goodtofufriday/megaman-battle--network-exe-chip-project/EXE 4 Advance Chips/Advance Chip Missing Labels/Black_Barrier_JPN.png

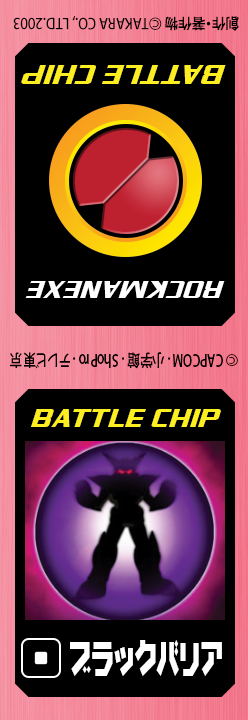
EXE 4 Advance Chips/Advance Chip Missing Labels/Black_Barrier_JPN.png
