goodtofufriday/megaman-battle--network-exe-chip-project/EXE 4 Advance Chips/Advance Chip Missing Labels/BurnerMan_ENG.png

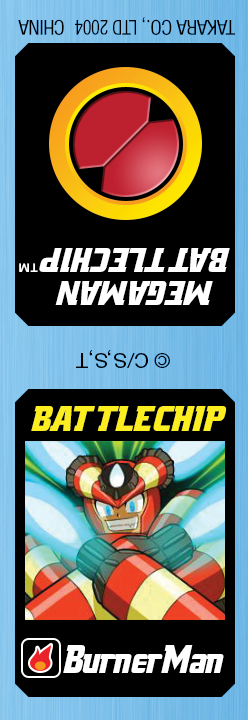
EXE 4 Advance Chips/Advance Chip Missing Labels/BurnerMan_ENG.png
