goodtofufriday/megaman-battle--network-exe-chip-project/EXE 4 Advance Chips/Advance Duo+GrandPrix Power Patch/image.png

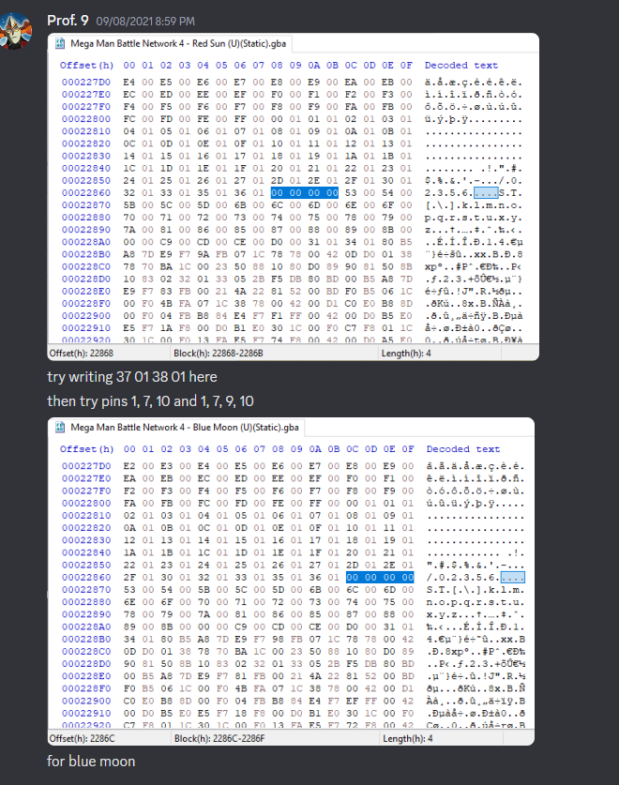
EXE 4 Advance Chips/Advance Duo+GrandPrix Power Patch/image.png
