goodtofufriday/megaman-battle--network-exe-chip-project/Plug-In Pet/Plug-In Pet Labels/0.jpg

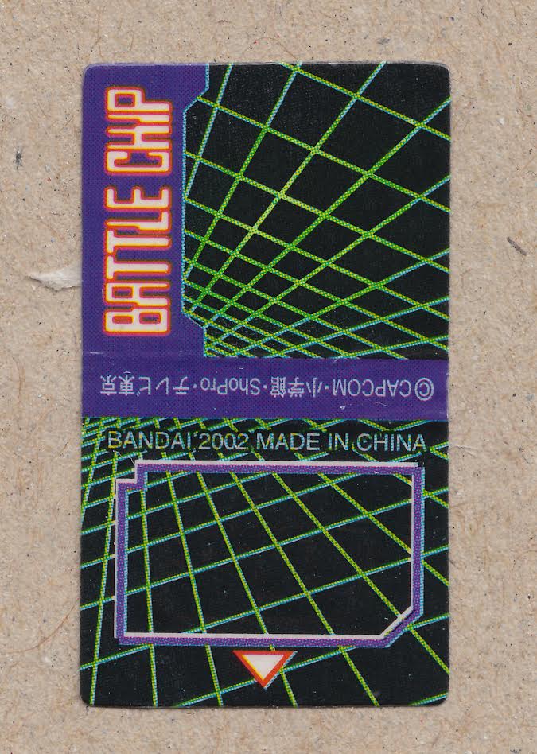
Plug-In Pet/Plug-In Pet Labels/0.jpg
