goodtofufriday/megaman-battle--network-exe-chip-project/Numbers/848.dxf

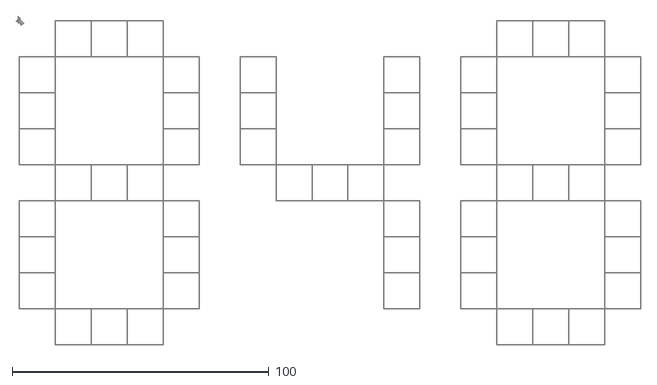
[picture p29: CAD file, 2023-03-07]
Numbers/848.dxf
243.4 x 127.9
