goodtofufriday/megaman-battle--network-exe-chip-project/Numbers/847.dxf

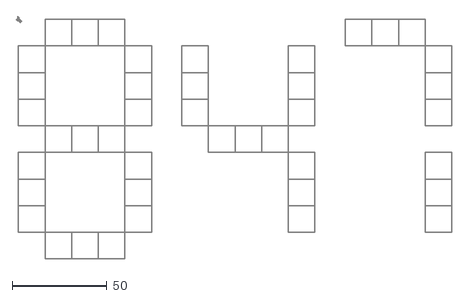
[picture p30: CAD file, 2023-03-07]
Numbers/847.dxf
229.6 x 128.0
