goodtofufriday/megaman-battle--network-exe-chip-project/Numbers/845.dxf

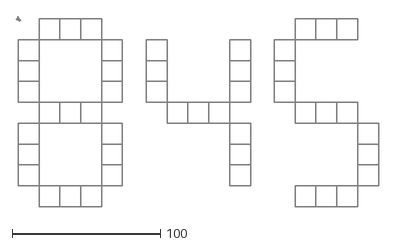
[picture p31: CAD file, 2023-03-07]
Numbers/845.dxf
244.0 x 128.2
