goodtofufriday/megaman-battle--network-exe-chip-project/Numbers/844.dxf

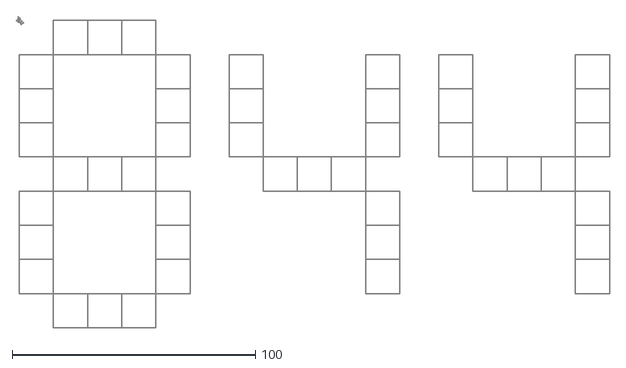
[picture p32: CAD file, 2023-03-07]
Numbers/844.dxf
244.0 x 128.2
