goodtofufriday/megaman-battle--network-exe-chip-project/Numbers/843.dxf

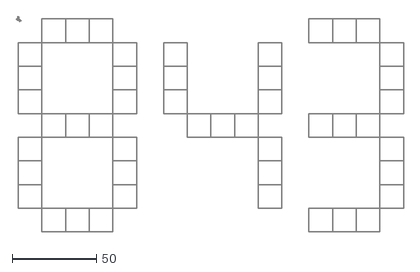
[picture p33: CAD file, 2023-03-07]
Numbers/843.dxf
230.1 x 128.3
