goodtofufriday/megaman-battle--network-exe-chip-project/Numbers/792.dxf

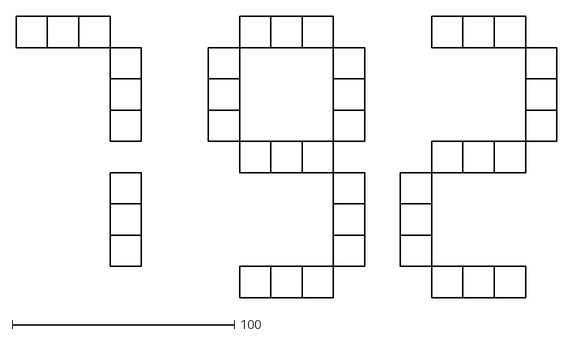
[picture p34: CAD file, 2023-03-07]
Numbers/792.dxf
243.0 x 126.6
