goodtofufriday/megaman-battle--network-exe-chip-project/Numbers/791.dxf

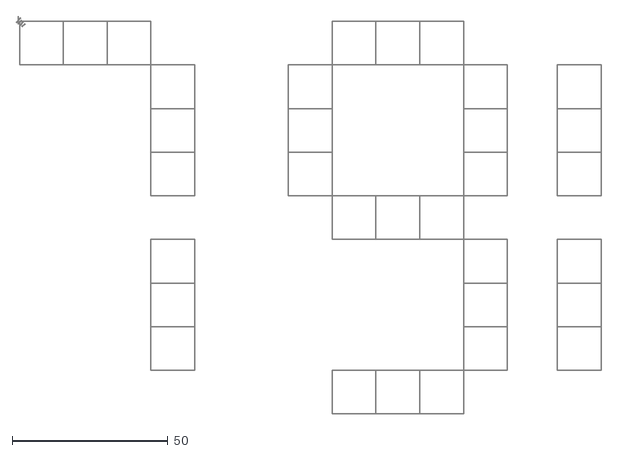
[picture p35: CAD file, 2023-03-07]
Numbers/791.dxf
188.0 x 127.9
