goodtofufriday/megaman-battle--network-exe-chip-project/Numbers/790.dxf

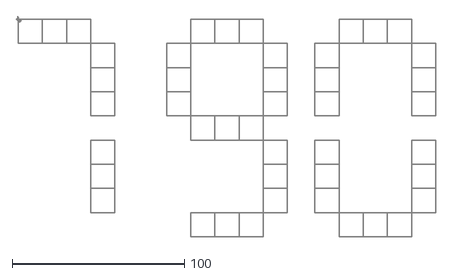
[picture p36: CAD file, 2023-03-07]
Numbers/790.dxf
243.8 x 128.1
