goodtofufriday/megaman-battle--network-exe-chip-project/Numbers/731.dxf

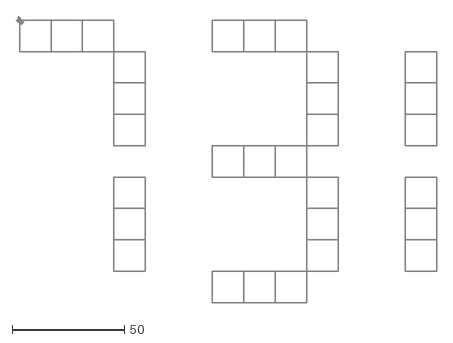
[picture p37: CAD file, 2023-03-07]
Numbers/731.dxf
187.4 x 127.7
