goodtofufriday/megaman-battle--network-exe-chip-project/Numbers/727.dxf

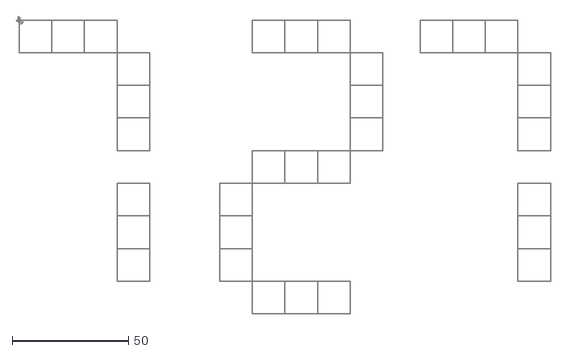
[picture p38: CAD file, 2023-03-07]
Numbers/727.dxf
229.6 x 128.0
