goodtofufriday/megaman-battle--network-exe-chip-project/Numbers/546.dxf

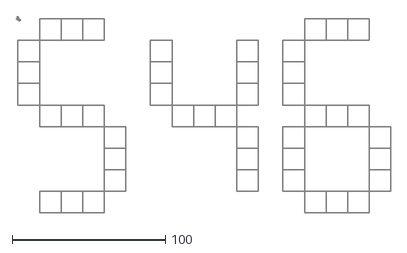
[picture p39: CAD file, 2023-03-07]
Numbers/546.dxf
244.2 x 128.3
