goodtofufriday/megaman-battle--network-exe-chip-project/Numbers/545.dxf

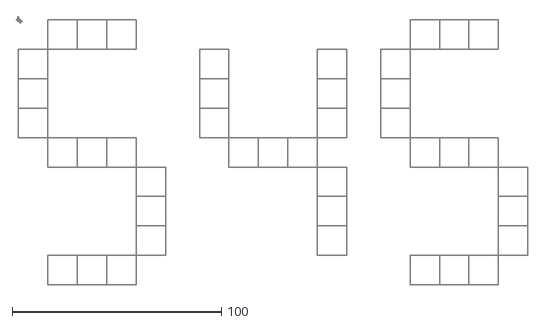
[picture p40: CAD file, 2023-03-07]
Numbers/545.dxf
244.8 x 128.6
