goodtofufriday/megaman-battle--network-exe-chip-project/Numbers/544.dxf

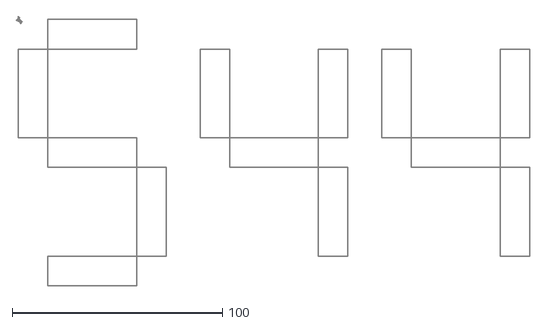
[picture p41: CAD file, 2023-03-07]
Numbers/544.dxf
244.3 x 128.2
