goodtofufriday/megaman-battle--network-exe-chip-project/Numbers/313.dxf

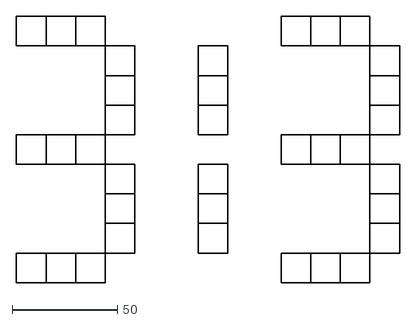
[picture p42: CAD file, 2023-03-07]
Numbers/313.dxf
182.1 x 126.6
