goodtofufriday/megaman-battle--network-exe-chip-project/Numbers/312.dxf

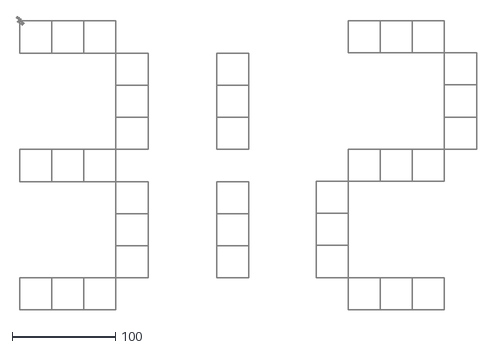
[picture p43: CAD file, 2023-03-07]
Numbers/312.dxf
446.1 x 284.9
