goodtofufriday/megaman-battle--network-exe-chip-project/Numbers/311.dxf

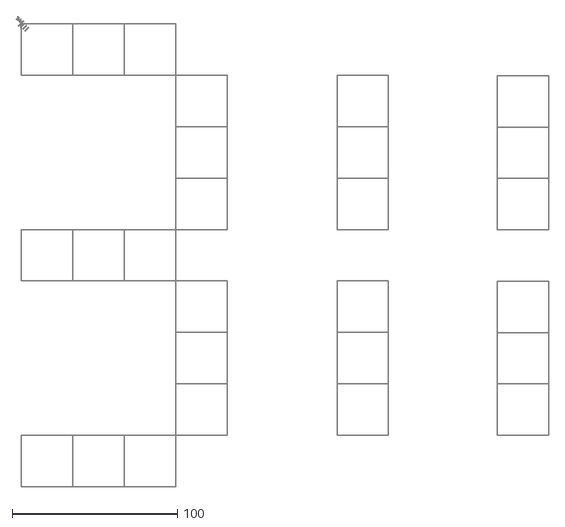
[picture p44: CAD file, 2023-03-07]
Numbers/311.dxf
321.7 x 284.2
