goodtofufriday/megaman-battle--network-exe-chip-project/Numbers/308.dxf

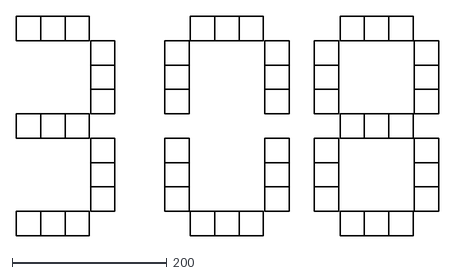
[picture p45: CAD file, 2023-03-07]
Numbers/308.dxf
545.8 x 283.5
