goodtofufriday/megaman-battle--network-exe-chip-project/Numbers/305.dxf

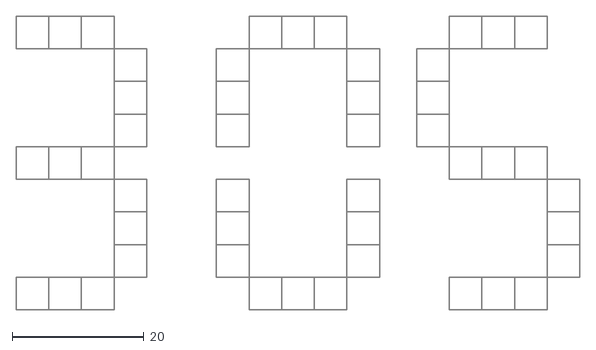
[picture p46: CAD file, 2023-03-07]
Numbers/305.dxf
85.7 x 44.6
