goodtofufriday/megaman-battle--network-exe-chip-project/Numbers/295.dxf

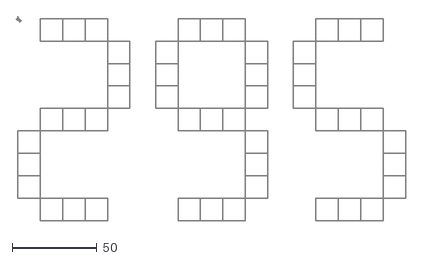
[picture p47: CAD file, 2023-03-07]
Numbers/295.dxf
230.1 x 120.8
