goodtofufriday/megaman-battle--network-exe-chip-project/Numbers/294.dxf

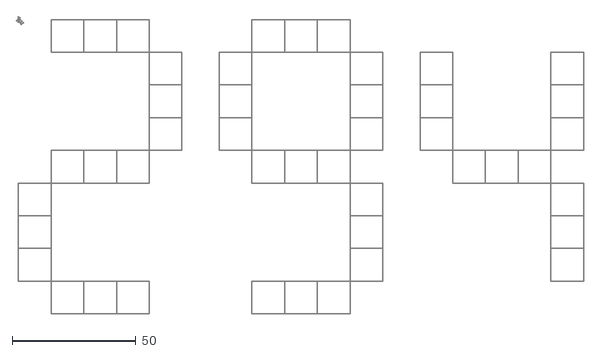
[picture p48: CAD file, 2023-03-07]
Numbers/294.dxf
229.4 x 120.4
