goodtofufriday/megaman-battle--network-exe-chip-project/Numbers/293.dxf

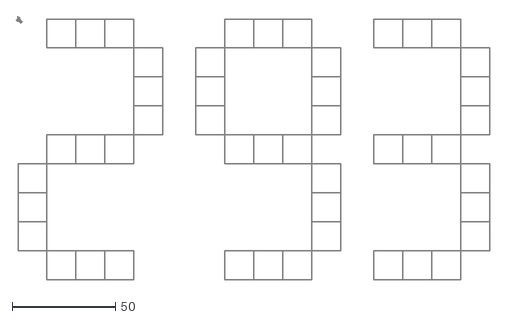
[picture p49: CAD file, 2023-03-07]
Numbers/293.dxf
229.3 x 127.7
