goodtofufriday/megaman-battle--network-exe-chip-project/Numbers/292.dxf

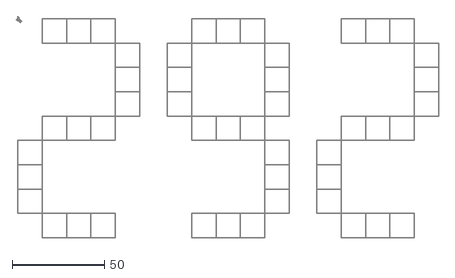
[picture p50: CAD file, 2023-03-07]
Numbers/292.dxf
229.1 x 120.2
