goodtofufriday/megaman-battle--network-exe-chip-project/Numbers/291.dxf

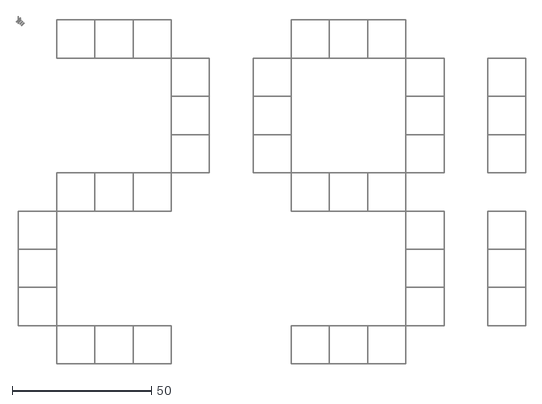
[picture p51: CAD file, 2023-03-07]
Numbers/291.dxf
182.8 x 124.7
