goodtofufriday/megaman-battle--network-exe-chip-project/Numbers/280.dxf

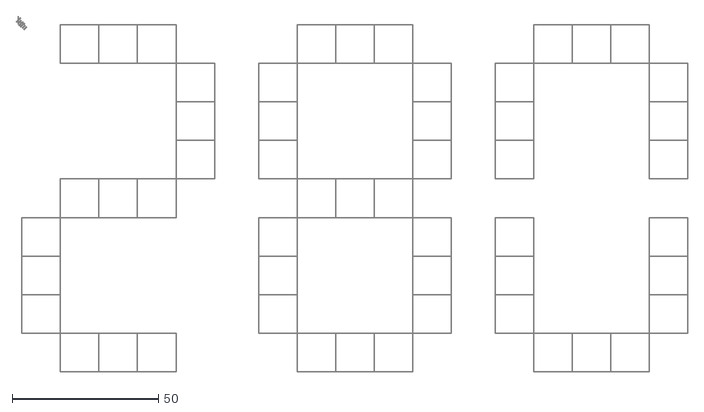
[picture p52: CAD file, 2023-03-07]
Numbers/280.dxf
229.8 x 121.6
