goodtofufriday/megaman-battle--network-exe-chip-project/Numbers/279.dxf

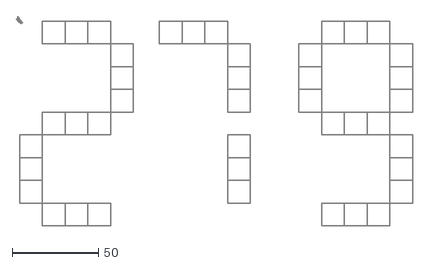
[picture p53: CAD file, 2023-03-07]
Numbers/279.dxf
229.7 x 121.5
