goodtofufriday/megaman-battle--network-exe-chip-project/Numbers/278.dxf

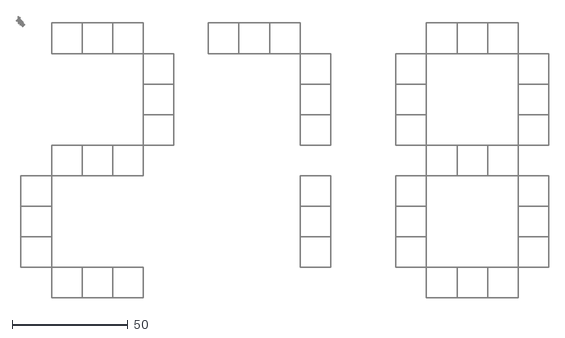
[picture p54: CAD file, 2023-03-07]
Numbers/278.dxf
229.5 x 121.4
