goodtofufriday/megaman-battle--network-exe-chip-project/Numbers/277.dxf

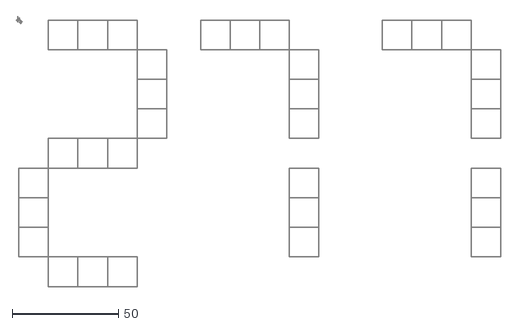
[picture p55: CAD file, 2023-03-07]
Numbers/277.dxf
228.6 x 127.4
