goodtofufriday/megaman-battle--network-exe-chip-project/Numbers/276.dxf

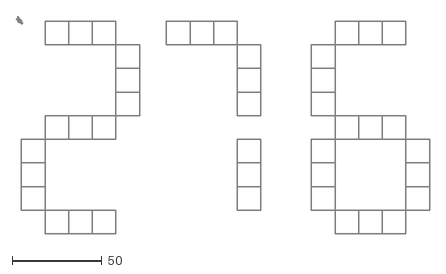
[picture p56: CAD file, 2023-03-07]
Numbers/276.dxf
229.8 x 121.1
