goodtofufriday/megaman-battle--network-exe-chip-project/Numbers/263.dxf

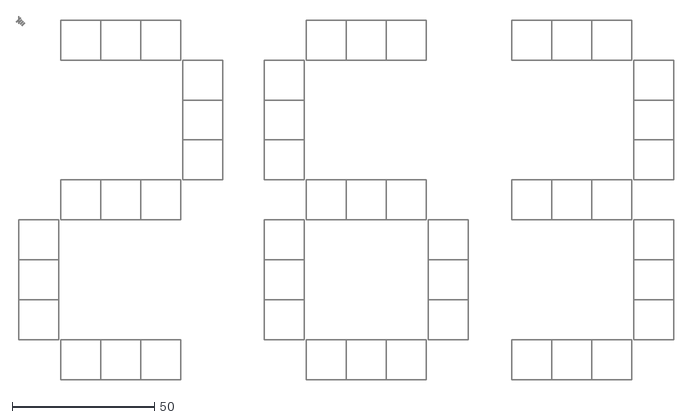
[picture p57: CAD file, 2023-03-07]
Numbers/263.dxf
230.8 x 127.7
