goodtofufriday/megaman-battle--network-exe-chip-project/Numbers/162.dxf

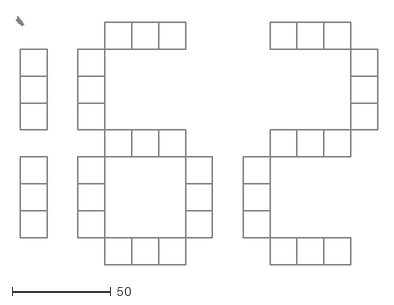
[picture p58: CAD file, 2023-03-07]
Numbers/162.dxf
182.6 x 125.4
