goodtofufriday/megaman-battle--network-exe-chip-project/Numbers/147.dxf

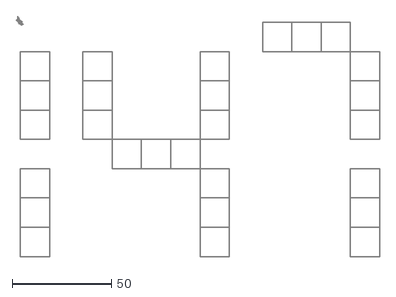
[picture p59: CAD file, 2023-03-07]
Numbers/147.dxf
182.7 x 120.7
