goodtofufriday/megaman-battle--network-exe-chip-project/Numbers/128.dxf

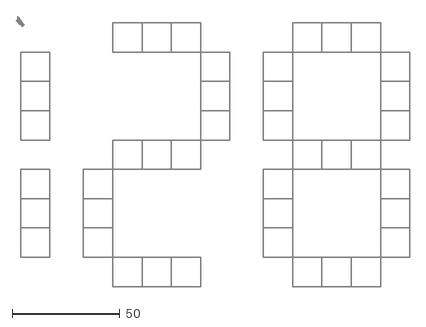
[picture p60: CAD file, 2023-03-07]
Numbers/128.dxf
182.9 x 125.5
