goodtofufriday/megaman-battle--network-exe-chip-project/Numbers/076.dxf

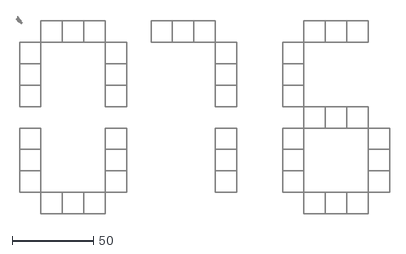
[picture p61: CAD file, 2023-03-07]
Numbers/076.dxf
229.5 x 121.4
