goodtofufriday/megaman-battle--network-exe-chip-project/Numbers/067.dxf

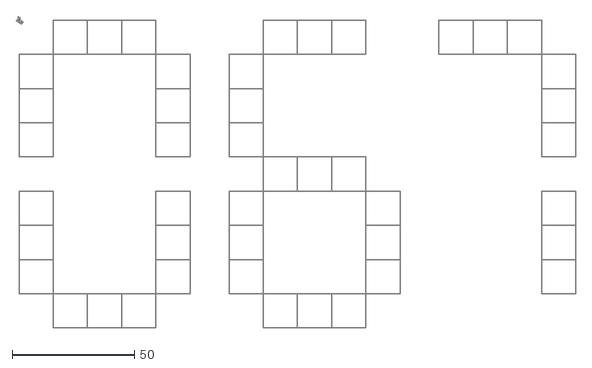
[picture p62: CAD file, 2023-03-07]
Numbers/067.dxf
229.1 x 127.7
