goodtofufriday/megaman-battle--network-exe-chip-project/Numbers/046.dxf

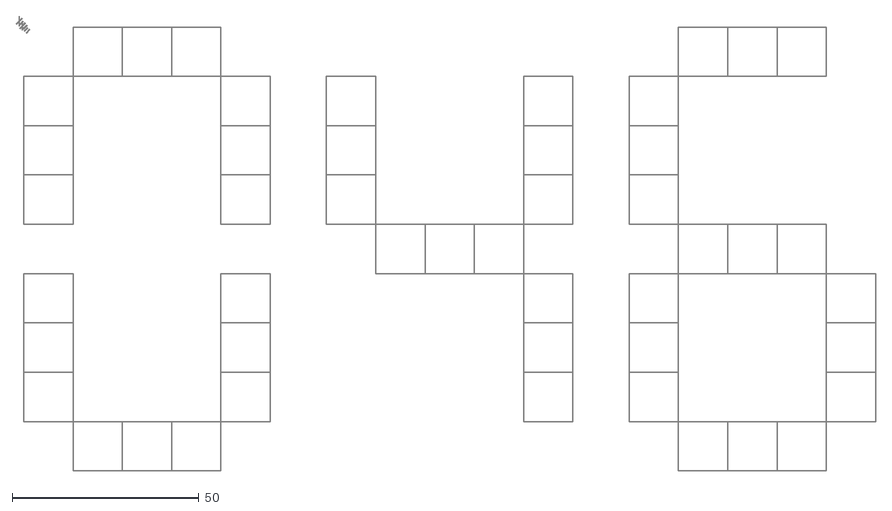
[picture p63: CAD file, 2023-03-07]
Numbers/046.dxf
229.8 x 121.6
