goodtofufriday/megaman-battle--network-exe-chip-project/Numbers/028.dxf

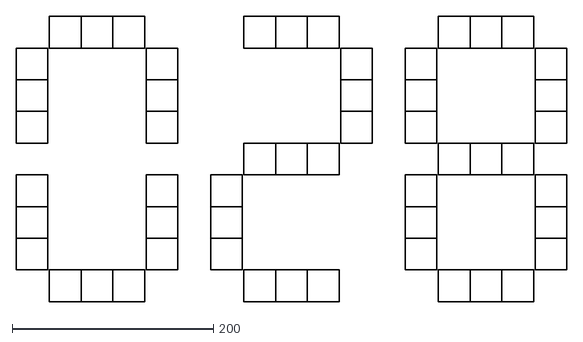
[picture p64: CAD file, 2023-03-07]
Numbers/028.dxf
547.3 x 283.5
