goodtofufriday/megaman-battle--network-exe-chip-project/Numbers/026.dxf

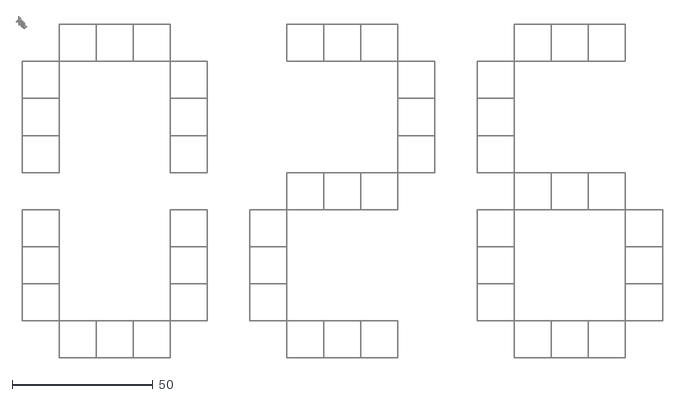
[picture p65: CAD file, 2023-03-07]
Numbers/026.dxf
229.5 x 121.4
