goodtofufriday/megaman-battle--network-exe-chip-project/Numbers/017.dxf

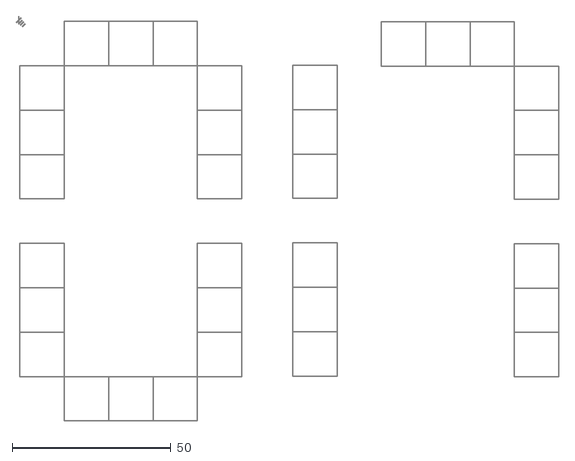
[picture p66: CAD file, 2023-03-07]
Numbers/017.dxf
171.1 x 127.7
