goodtofufriday/megaman-battle--network-exe-chip-project/Numbers/DXF Import Measurements/import_advance_dxf.PNG

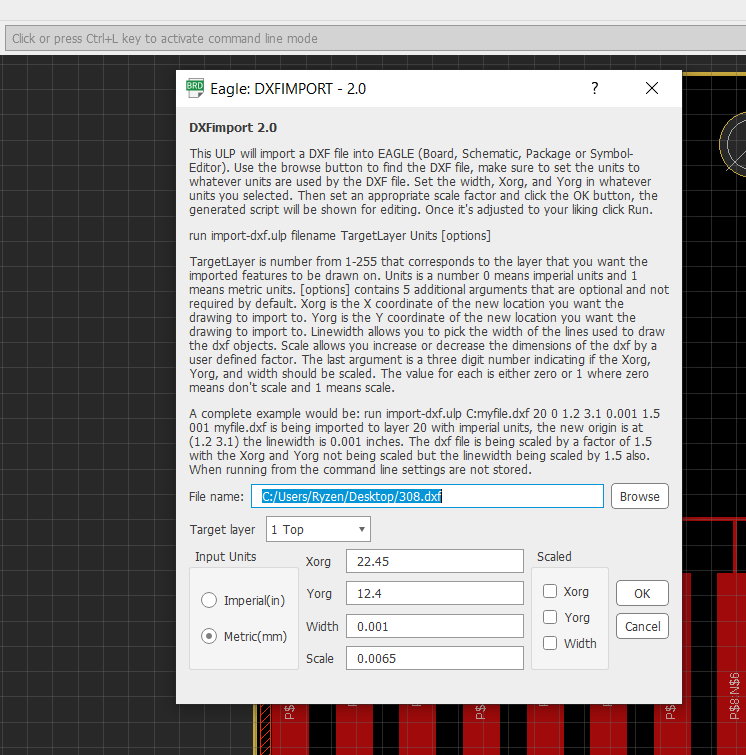
Numbers/DXF Import Measurements/import_advance_dxf.PNG
