goodtofufriday/megaman-battle--network-exe-chip-project/Numbers/DXF Import Measurements/Import_Link_dxf_Final.png

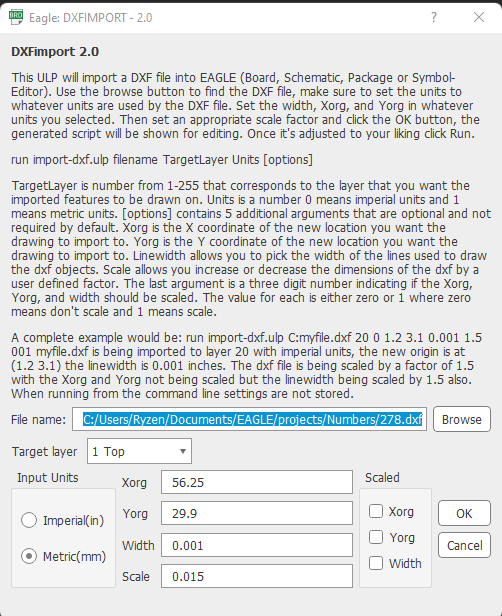
Numbers/DXF Import Measurements/Import_Link_dxf_Final.png
