goodtofufriday/megaman-battle--network-exe-chip-project/Numbers/DXF Import Measurements/Import_Link_dxf_Final_-_WITH_a_ONE.png

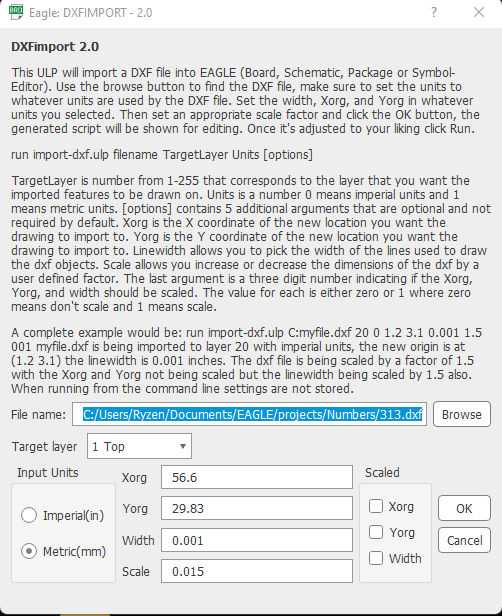
Numbers/DXF Import Measurements/Import_Link_dxf_Final_-_WITH_a_ONE.png
