goodtofufriday/megaman-battle--network-exe-chip-project/EXE 6 Link Chips/Link Dip Chip/beast.sch

## EAGLE design EXE 6 Link Chips/Link Dip Chip/beast.sch (2023-03-08)

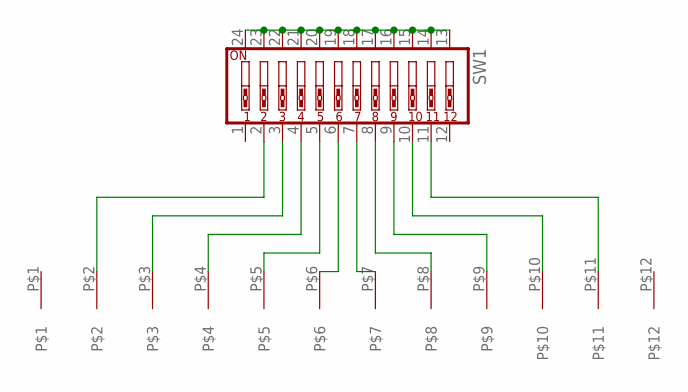
[picture p80: schematic beast.sch]

Parts:
SW1: SW_DIP-12; EDG-12
U$1: BEAST

Connections:
unnamed: SW1.13, SW1.14, SW1.15, SW1.16, SW1.17, SW1.18, SW1.19, SW1.20, SW1.21, SW1.22, SW1.23, SW1.24
unnamed: SW1.2, U$1.P$2
unnamed: SW1.3, U$1.P$3
unnamed: SW1.10, U$1.P$10
unnamed: SW1.5, U$1.P$5
unnamed: SW1.6, U$1.P$6
unnamed: SW1.7, U$1.P$7
unnamed: SW1.8, U$1.P$8
unnamed: SW1.9, U$1.P$9
unnamed: SW1.11, U$1.P$11
unnamed: SW1.4, U$1.P$4
