goodtofufriday/megaman-battle--network-exe-chip-project/EXE 6 Link Chips/Link Navi IC Repro/beast_navi_small_ic_curved_repro.sch

## EAGLE design EXE 6 Link Chips/Link Navi IC Repro/beast_navi_small_ic_curved_repro.sch (2023-03-08)

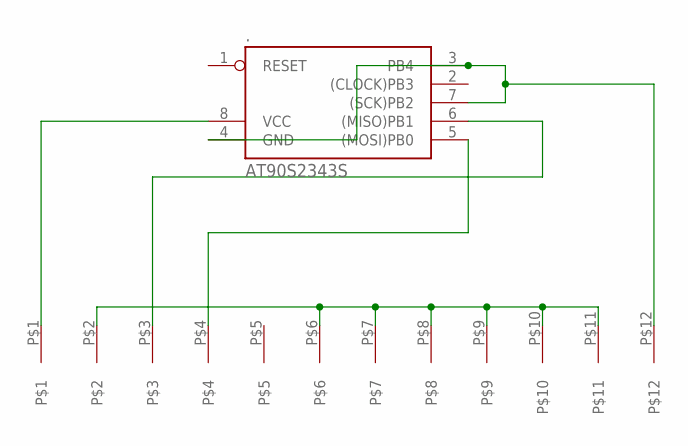
[picture p81: schematic beast_navi_small_ic_curved_repro.sch]

Parts:
.: AT90S2343S; SOIC8
U$1: BEAST

Connections:
unnamed: U$1.P$2, U$1.P$6, U$1.P$7, U$1.P$8, U$1.P$9, U$1.P$10, U$1.P$11
unnamed: ..3 (PB4), ..4 (GND), ..7 ((SCK)PB2), U$1.P$12
unnamed: ..8 (VCC), U$1.P$1
unnamed: ..6 ((MISO)PB1), U$1.P$3
unnamed: ..5 ((MOSI)PB0), U$1.P$4
