goodtofufriday/megaman-battle--network-exe-chip-project/EXE 6 Link Chips/Link Navi IC Standalone/beast_navi_small_ic.sch

## EAGLE design EXE 6 Link Chips/Link Navi IC Standalone/beast_navi_small_ic.sch (2023-03-08)

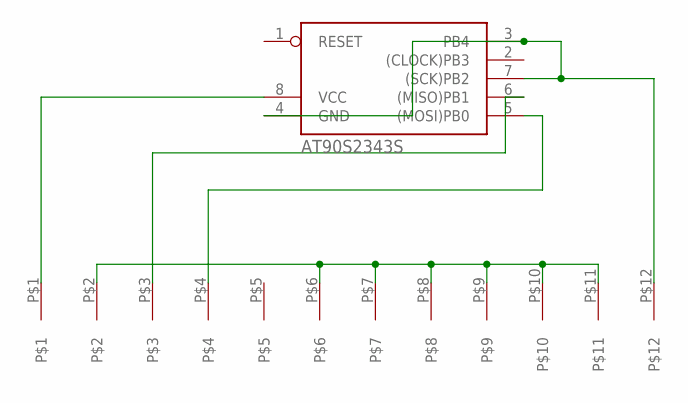
[picture p82: schematic beast_navi_small_ic.sch]

Parts:
IC1: AT90S2343S; SOIC8
U$1: BEAST

Connections:
unnamed: U$1.P$2, U$1.P$6, U$1.P$7, U$1.P$8, U$1.P$9, U$1.P$10, U$1.P$11
unnamed: IC1.3 (PB4), IC1.4 (GND), IC1.7 ((SCK)PB2), U$1.P$12
unnamed: IC1.6 ((MISO)PB1), U$1.P$3
unnamed: IC1.8 (VCC), U$1.P$1
unnamed: IC1.5 ((MOSI)PB0), U$1.P$4
