goodtofufriday/megaman-battle--network-exe-chip-project/Plug-In Pet/Plug-In Pet Dip Chip/Plug-In_Pet_Dip_Chip.sch

## EAGLE design Plug-In Pet/Plug-In Pet Dip Chip/Plug-In_Pet_Dip_Chip.sch (2023-03-07)

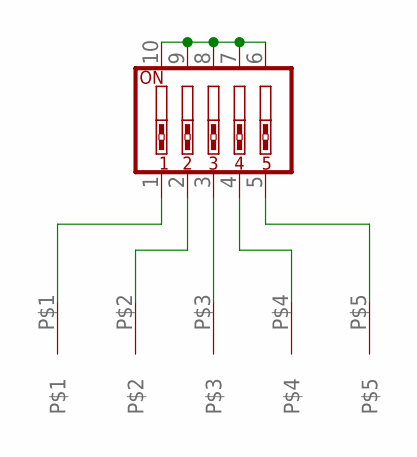
[picture p84: schematic Plug-In_Pet_Dip_Chip.sch]

Parts:
SW2: SW_DIP-5; EDG-05
U$1: PLUGINPET

Connections:
unnamed: SW2.6, SW2.7, SW2.8, SW2.9, SW2.10
unnamed: SW2.1, U$1.P$1
unnamed: SW2.2, U$1.P$2
unnamed: SW2.3, U$1.P$3
unnamed: SW2.4, U$1.P$4
unnamed: SW2.5, U$1.P$5
